mskarha/le-baton/img/electronics/IMG_20210120_174454.jpg

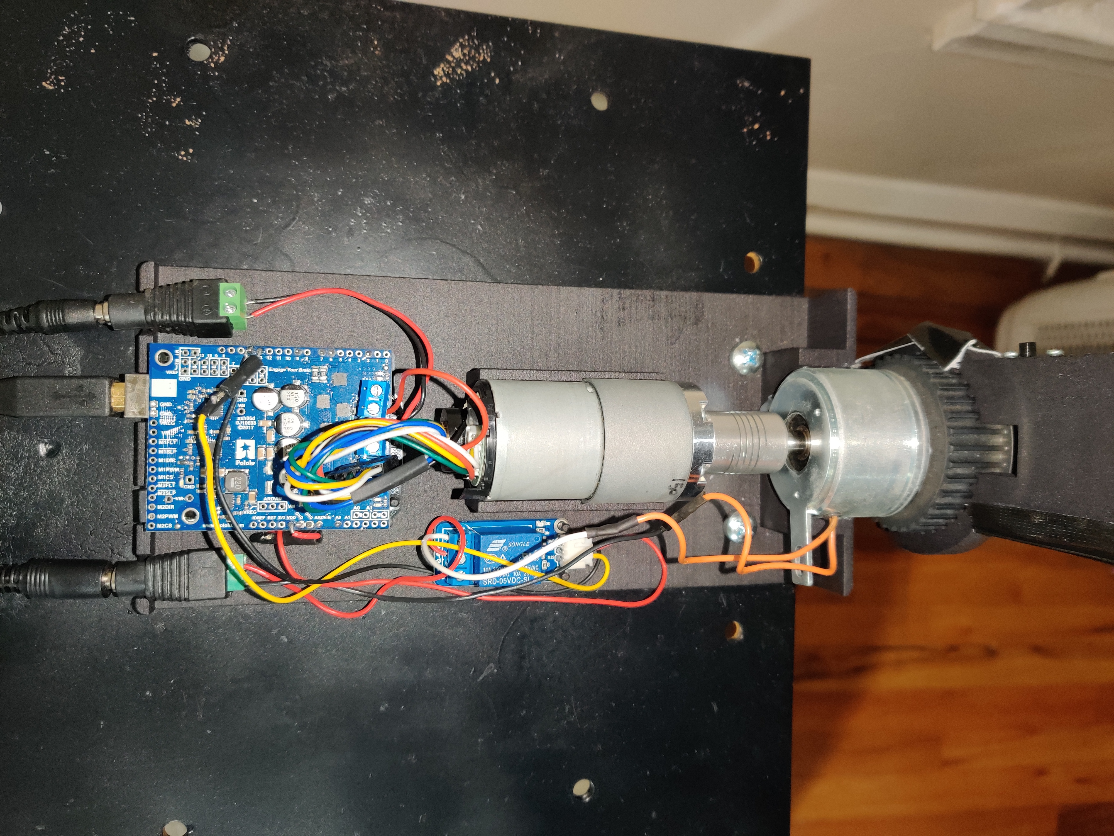
img/electronics/IMG_20210120_174454.jpg
