mskarha/le-baton/img/long exposure/DSC_0009.JPG

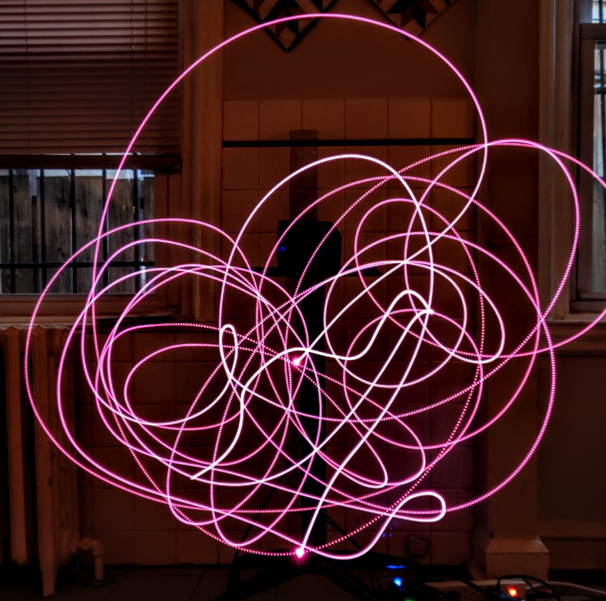
img/long exposure/DSC_0009.JPG
