mskarha/le-baton/img/long exposure/DSC_0010 (1).JPG

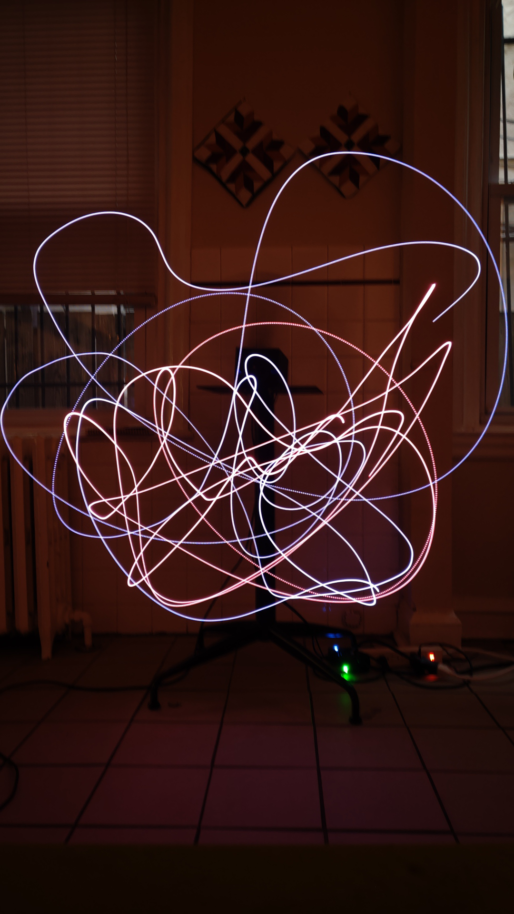
img/long exposure/DSC_0010 (1).JPG
