mskarha/le-baton/img/long exposure/DSC_0014.JPG

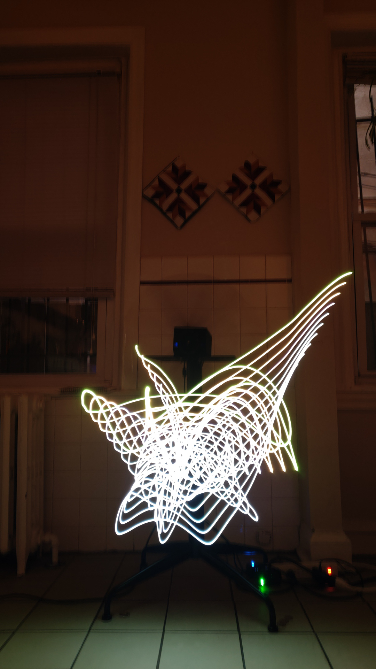
img/long exposure/DSC_0014.JPG
