mskarha/le-baton/img/long exposure/IMG_20210515_141202.jpg

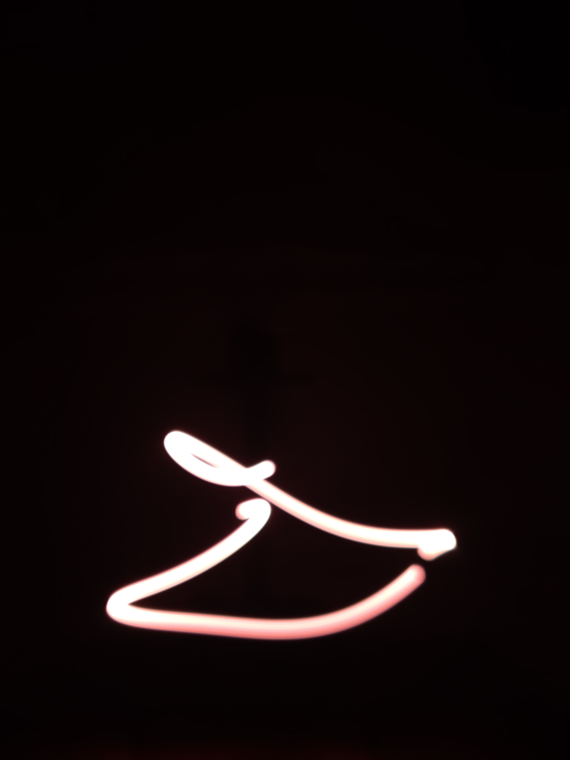
img/long exposure/IMG_20210515_141202.jpg
