mskarha/le-baton/img/long exposure/IMG_20210515_141343.jpg

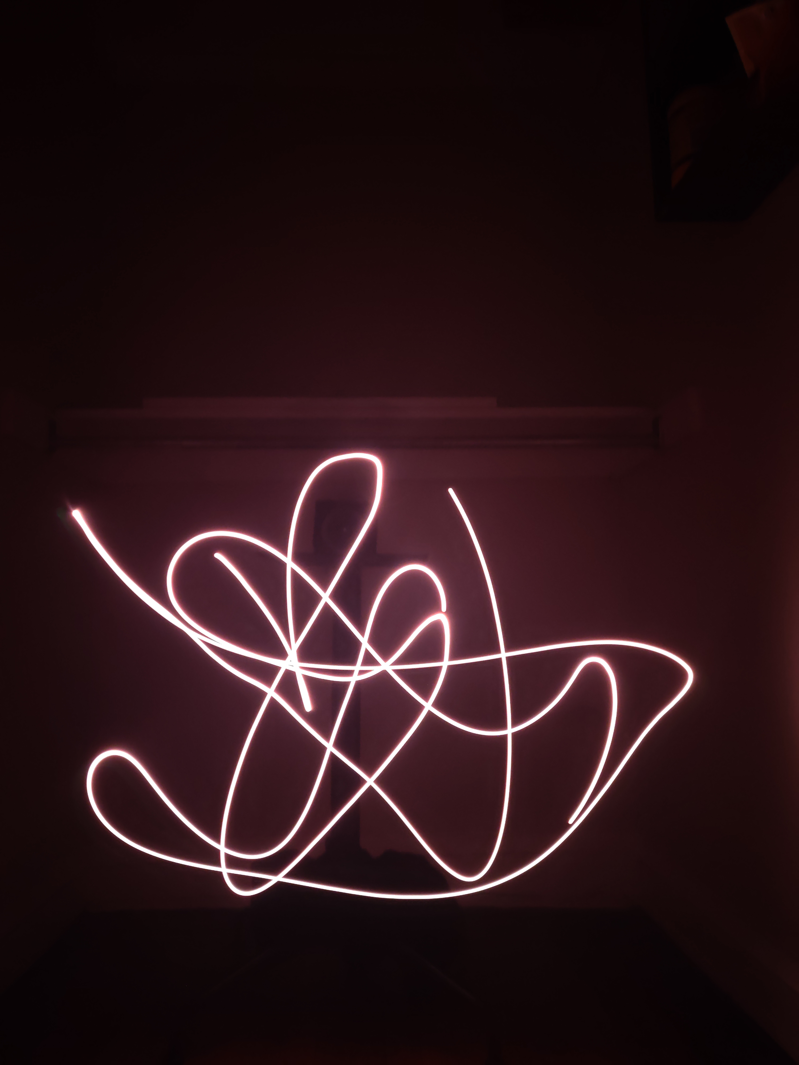
img/long exposure/IMG_20210515_141343.jpg
