mskarha/le-baton/img/long exposure/IMG_20210515_141452.jpg

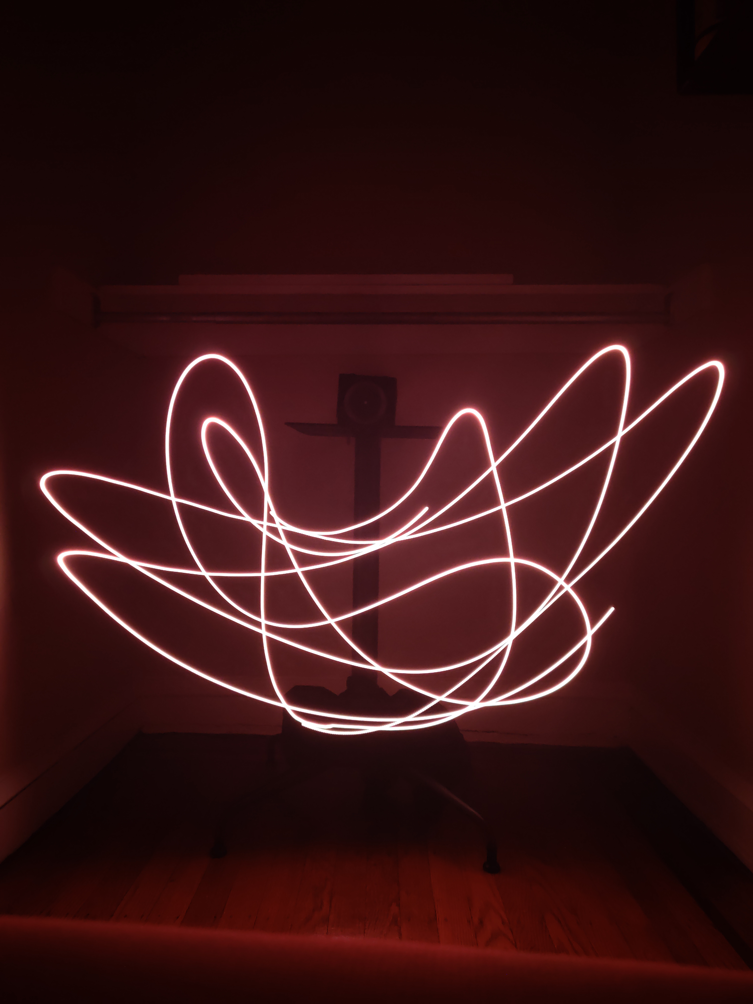
img/long exposure/IMG_20210515_141452.jpg
