mskarha/le-baton/img/long exposure/IMG_20210515_141930 (1).jpg

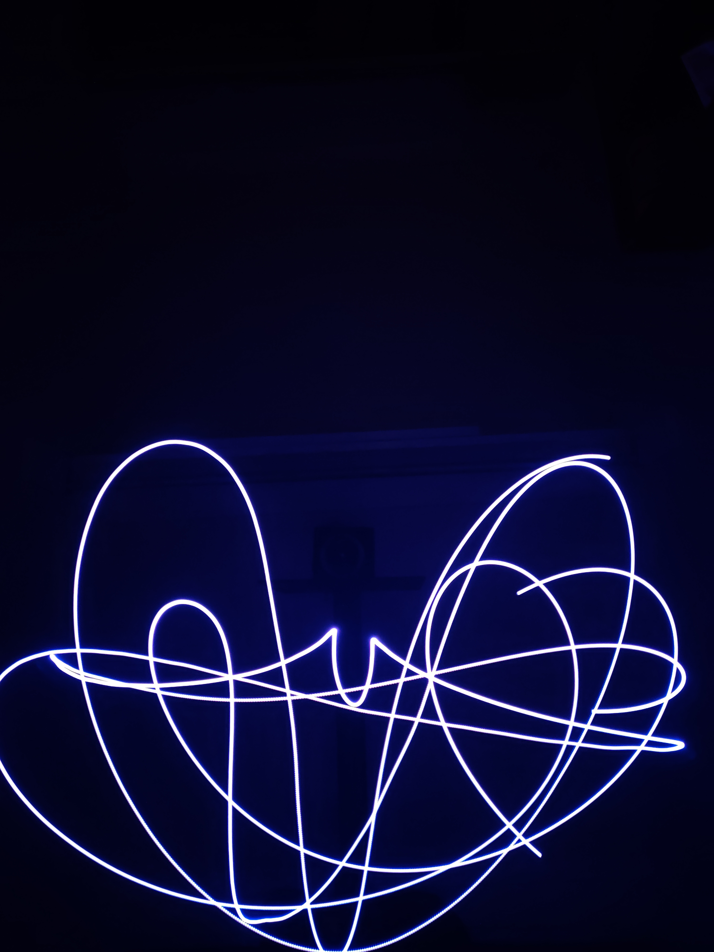
img/long exposure/IMG_20210515_141930 (1).jpg
