mskarha/le-baton/img/long exposure/IMG_20210515_142038.jpg

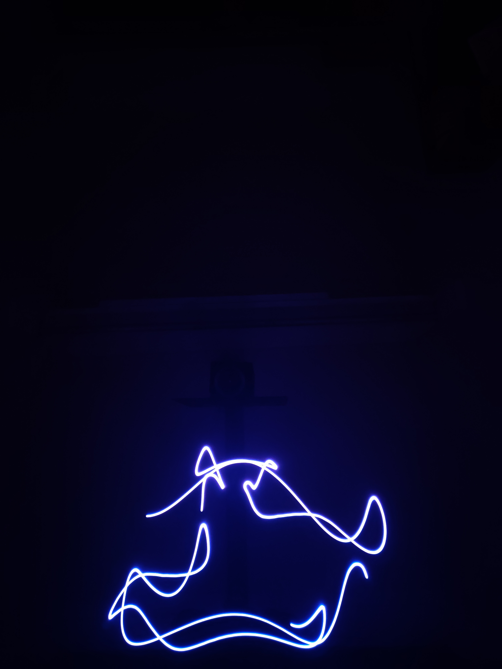
img/long exposure/IMG_20210515_142038.jpg
