mskarha/le-baton/img/long exposure/IMG_20210515_142056.jpg

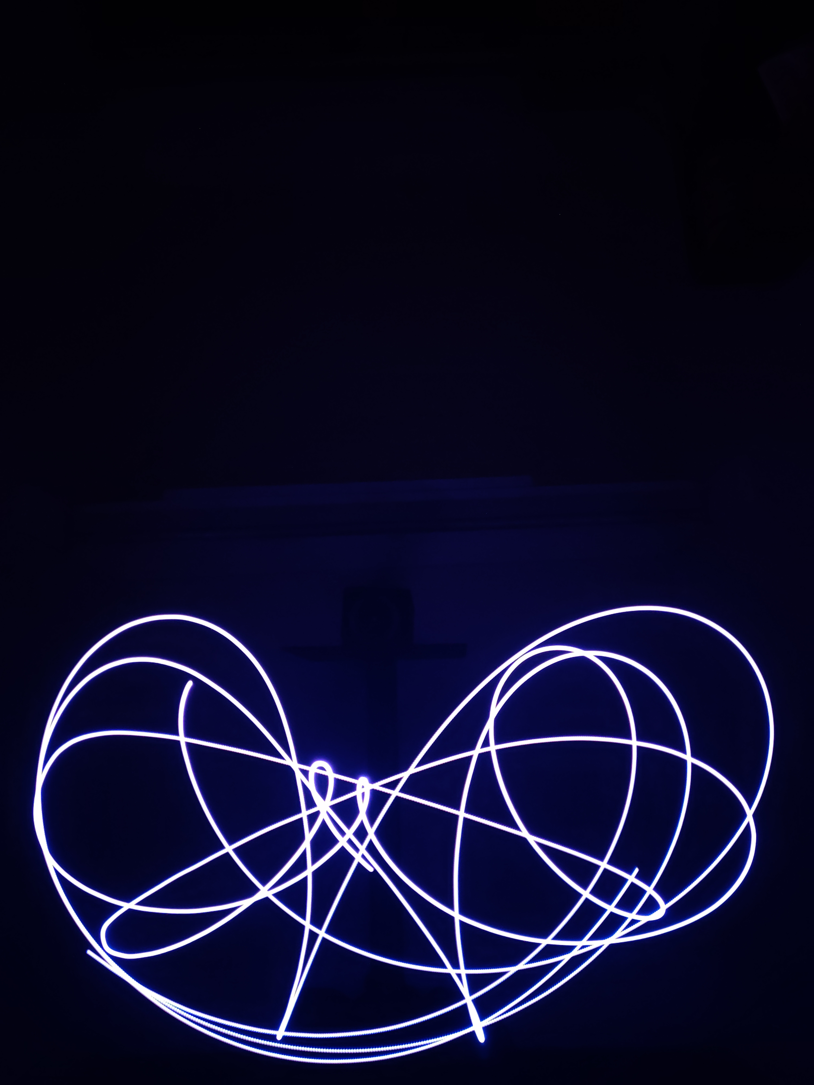
img/long exposure/IMG_20210515_142056.jpg
