mskarha/le-baton/img/long exposure/IMG_20210515_142231.jpg

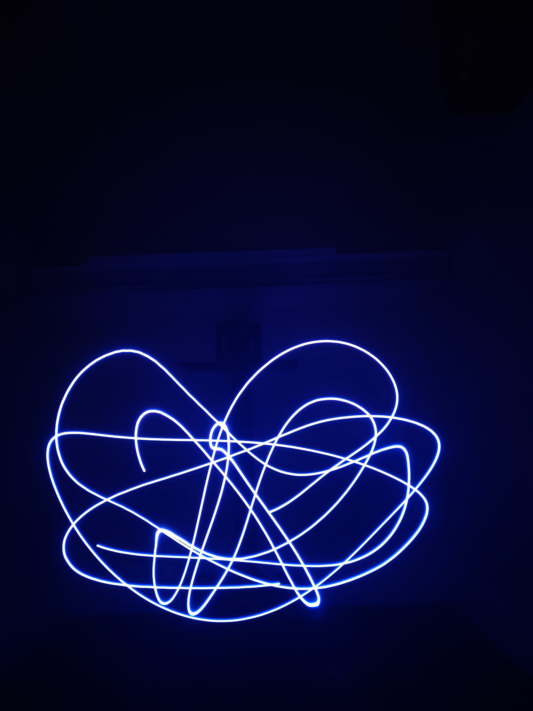
img/long exposure/IMG_20210515_142231.jpg
