mskarha/le-baton/img/long exposure/IMG_20210515_142607.jpg

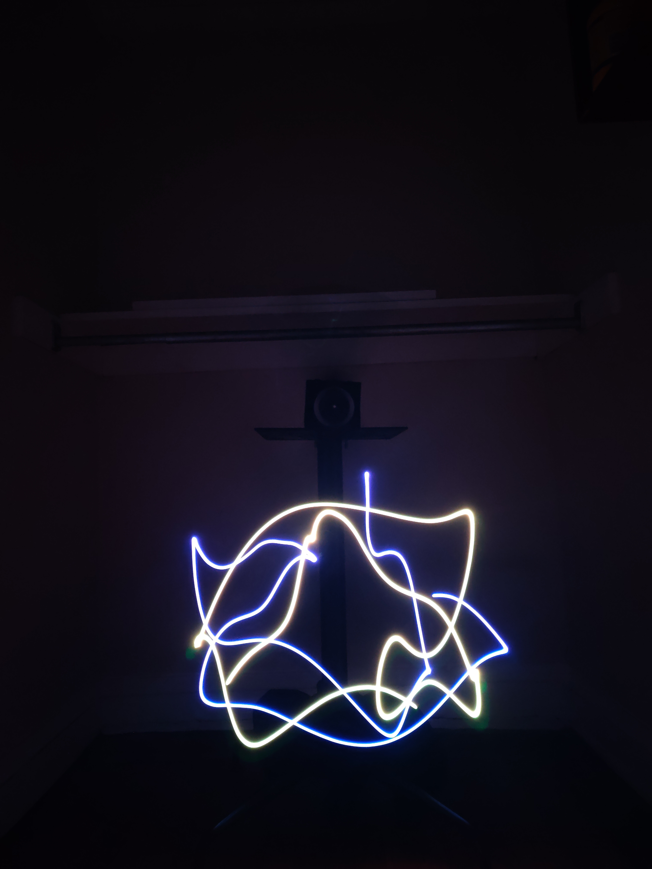
img/long exposure/IMG_20210515_142607.jpg
