mskarha/le-baton/img/long exposure/IMG_20210515_143024.jpg

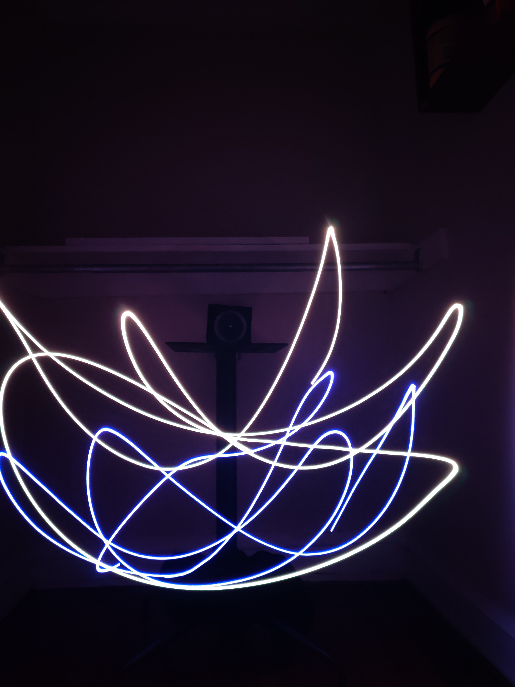
img/long exposure/IMG_20210515_143024.jpg
