mskarha/le-baton/img/long exposure/IMG_20210515_143225 (2).jpg

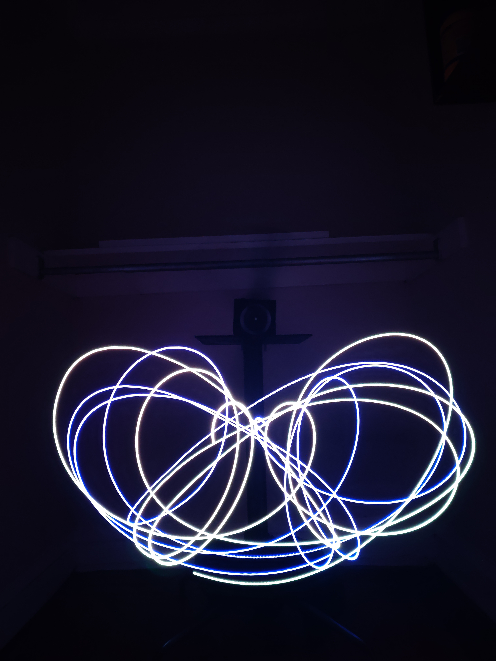
img/long exposure/IMG_20210515_143225 (2).jpg
