mskarha/le-baton/img/long exposure/IMG_20210515_143409.jpg

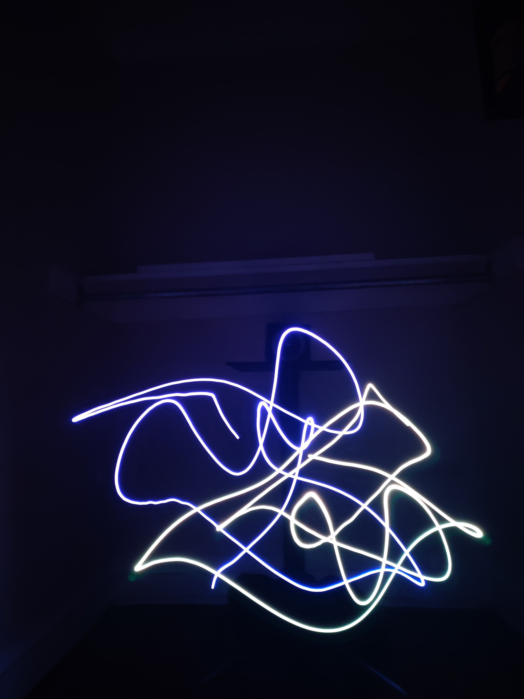
img/long exposure/IMG_20210515_143409.jpg
